ScatteredDrifter/Quasar-67/plate/Top-Plate-rocket-botkeys.dxf

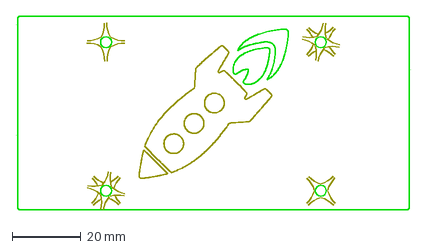
[picture p16: CAD file, 2023-08-10]
plate/Top-Plate-rocket-botkeys.dxf
114.3 x 56.2 mm
