ScatteredDrifter/Quasar-67/plate/Top-Plate-rocket-4x5-isothumbs.dxf

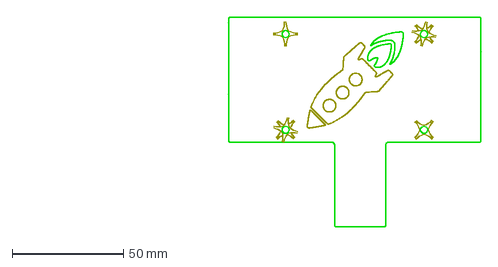
[picture p17: CAD file, 2023-03-31]
plate/Top-Plate-rocket-4x5-isothumbs.dxf
209.6 x 94.8 mm
