ScatteredDrifter/Quasar-67/plate/Top-Plate-quasar-4x5-isothumbs.dxf

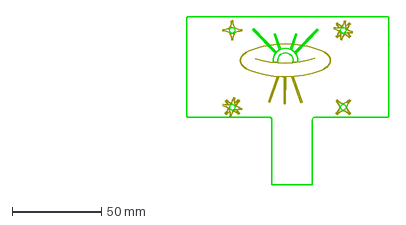
[picture p18: CAD file, 2023-03-31]
plate/Top-Plate-quasar-4x5-isothumbs.dxf
209.6 x 94.8 mm
